geg-tech/brew-keeb/Production/top shell left half.stl

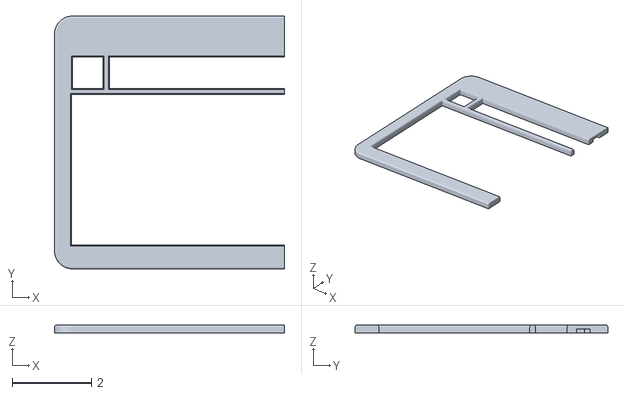
[picture p15: CAD file, 2026-03-29]
Production/top shell left half.stl
5.79 x 6.37 x 0.2
