geg-tech/brew-keeb/CAD/Split Parts/top shell right half.step

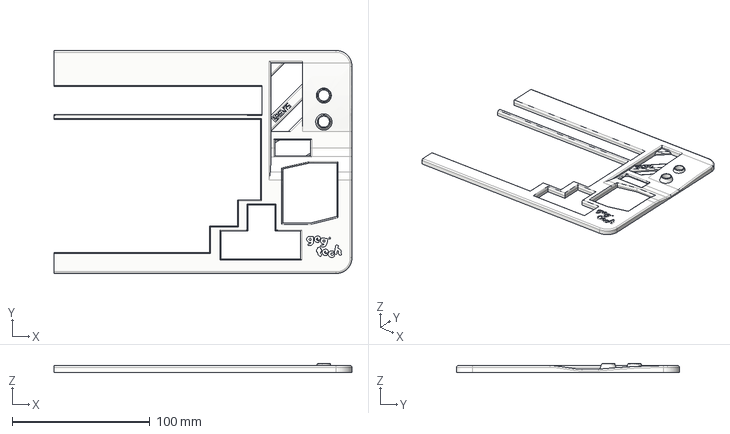
[picture p16: CAD file, 2026-03-26]
CAD/Split Parts/top shell right half.step
216.2 x 161.8 x 6.67 mm
