geg-tech/brew-keeb/Production/plate right half.stl

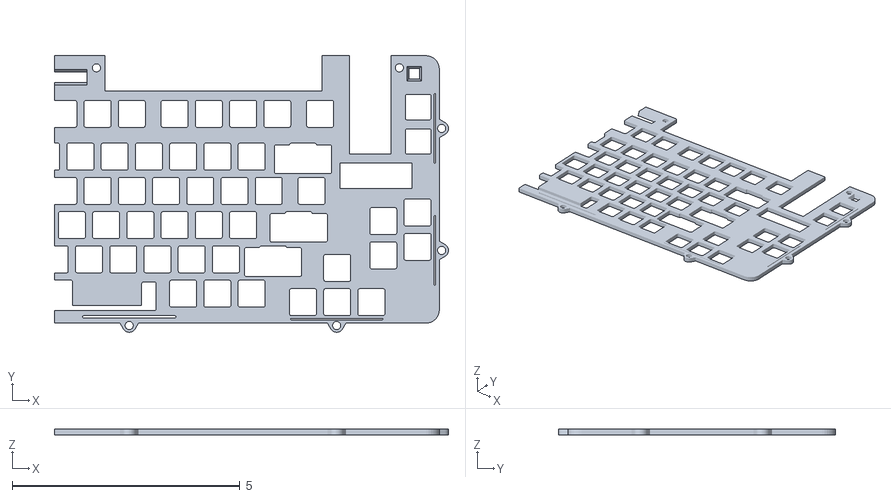
[picture p17: CAD file, 2026-03-29]
Production/plate right half.stl
8.64 x 6.07 x 0.125
