geg-tech/brew-keeb/Production/bottom shell left hald.stl

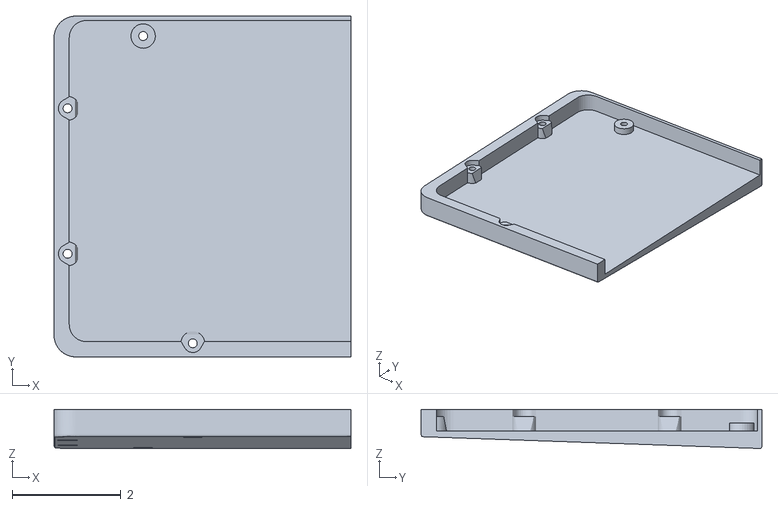
[picture p18: CAD file, 2026-03-29]
Production/bottom shell left hald.stl
5.46 x 6.27 x 0.718
