geg-tech/brew-keeb/Production/knob v3.stl

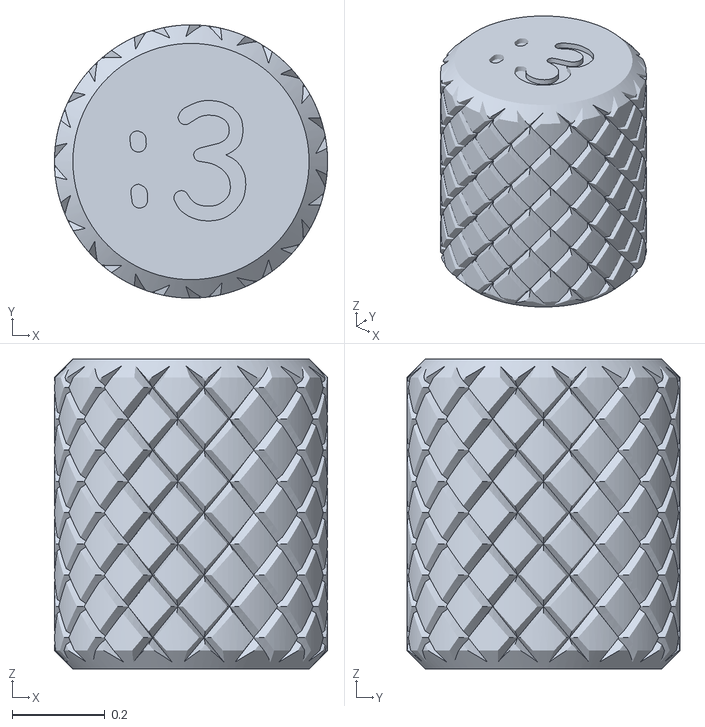
[picture p19: CAD file, 2026-03-29]
Production/knob v3.stl
0.591 x 0.591 x 0.67
