geg-tech/brew-keeb/PCB/brew-keeb-v2.kicad_sch

## KiCad design PCB/brew-keeb-v2.kicad_sch (2026-03-29)

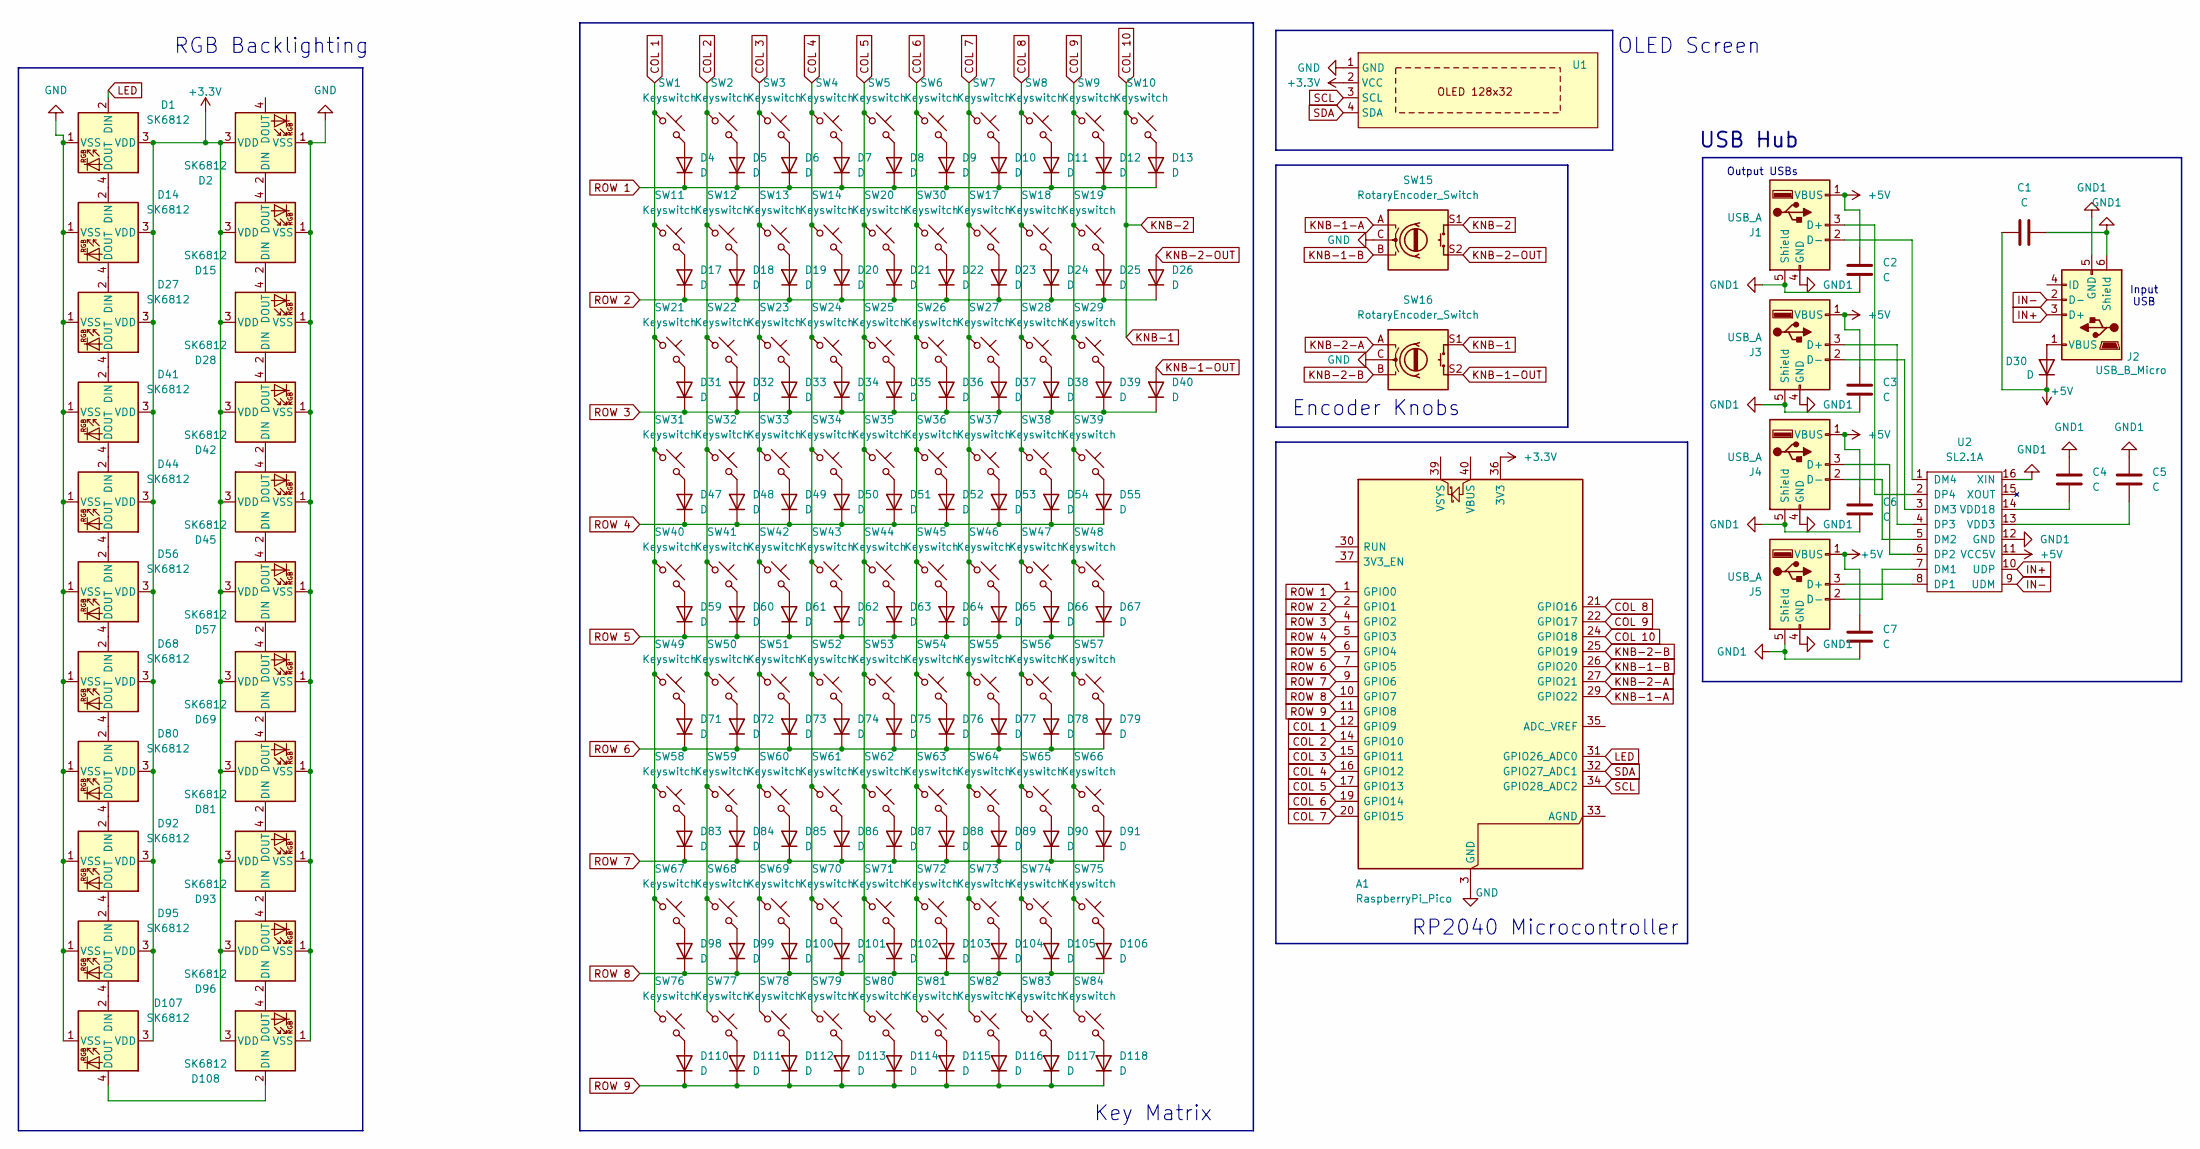
[picture p20: schematic brew-keeb-v2.kicad_sch]

Parts:
A1: RaspberryPi_Pico; RaspberryPi_Pico_Common_Unspecified
C1, C2, C3, C4, C5, C6, C7: C; C_1206_3216Metric_Pad1.33x1.80mm_HandSolder
D1, D2, D14, D15, D27, D28, D41, D42, D44, D45, D56, D57, D68, D69, D80, D81, D92, D93, D95, D96, D107, D108: SK6812; LED_SK6812_PLCC4_5.0x5.0mm_P3.2mm
D4, D5, D6, D7, D8, D9, D10, D11, D12, D13, D17, D18, D19, D20, D21, D22, D23, D24, D25, D26, D30, D31, D32, D33, D34, D35, D36, D37, D38, D39, D40, D47, D48, D49, D50, D51, D52, D53, D54, D55, D59, D60, D61, D62, D63, D64, D65, D66, D67, D71, D72, D73, D74, D75, D76, D77, D78, D79, D83, D84, D85, D86, D87, D88, D89, D90, D91, D98, D99, D100, D101, D102, D103, D104, D105, D106, D110, D111, D112, D113, D114, D115, D116, D117, D118: D; D_DO-35_SOD27_P7.62mm_Horizontal
J1, J3, J4, J5: USB_A; USB_A_Molex_67643_Horizontal
J2: USB_B_Micro; USB_Micro-B_Wuerth_629105150521
SW1, SW2, SW3, SW4, SW5, SW6, SW7, SW8, SW9, SW10, SW11, SW12, SW13, SW14, SW17, SW18, SW19, SW20, SW21, SW22, SW23, SW24, SW25, SW26, SW27, SW28, SW29, SW30, SW31, SW32, SW33, SW34, SW35, SW36, SW37, SW38, SW39, SW40, SW41, SW42, SW43, SW44, SW45, SW46, SW47, SW48, SW49, SW50, SW51, SW52, SW53, SW54, SW55, SW56, SW57, SW58, SW59, SW60, SW61, SW62, SW63, SW64, SW65, SW66, SW67, SW68, SW69, SW70, SW71, SW72, SW73, SW74, SW75, SW76, SW77, SW78, SW79, SW80, SW81, SW82, SW83, SW84: Keyswitch; SW_Cherry_MX_1.00u_PCB
SW15, SW16: RotaryEncoder_Switch; RotaryEncoder_Alps_EC11E-Switch_Vertical_H20mm
U1: SSD1306-0.91-OLED-4pin-128x32
U2: SL2.1A; SOIC-16_4.55x10.3mm_P1.27mm

Connections:
+3.3V: A1.36 (3V3), D1.3 (VDD), D2.3 (VDD), D14.3 (VDD), D15.3 (VDD), D27.3 (VDD), D28.3 (VDD), D41.3 (VDD), D42.3 (VDD), D44.3 (VDD), D45.3 (VDD), D56.3 (VDD), D57.3 (VDD), D68.3 (VDD), D69.3 (VDD), D80.3 (VDD), D81.3 (VDD), D92.3 (VDD), D93.3 (VDD), D95.3 (VDD), D96.3 (VDD), D107.3 (VDD), D108.3 (VDD), U1.2 (VCC)
+5V: C1.1, C2.1, C3.1, C6.1, C7.1, D30.1 (K), J1.1 (VBUS), J3.1 (VBUS), J4.1 (VBUS), J5.1 (VBUS), U2.11 (VCC5V)
COL 1: A1.12 (GPIO9), SW1.1, SW11.1, SW21.1, SW31.1, SW40.1, SW49.1, SW58.1, SW67.1, SW76.1
COL 2: A1.14 (GPIO10), SW2.1, SW12.1, SW22.1, SW32.1, SW41.1, SW50.1, SW59.1, SW68.1, SW77.1
COL 3: A1.15 (GPIO11), SW3.1, SW13.1, SW23.1, SW33.1, SW42.1, SW51.1, SW60.1, SW69.1, SW78.1
COL 4: A1.16 (GPIO12), SW4.1, SW14.1, SW24.1, SW34.1, SW43.1, SW52.1, SW61.1, SW70.1, SW79.1
COL 5: A1.17 (GPIO13), SW5.1, SW20.1, SW25.1, SW35.1, SW44.1, SW53.1, SW62.1, SW71.1, SW80.1
COL 6: A1.19 (GPIO14), SW6.1, SW26.1, SW30.1, SW36.1, SW45.1, SW54.1, SW63.1, SW72.1, SW81.1
COL 7: A1.20 (GPIO15), SW7.1, SW17.1, SW27.1, SW37.1, SW46.1, SW55.1, SW64.1, SW73.1, SW82.1
COL 8: A1.21 (GPIO16), SW8.1, SW18.1, SW28.1, SW38.1, SW47.1, SW56.1, SW65.1, SW74.1, SW83.1
COL 9: A1.22 (GPIO17), SW9.1, SW19.1, SW29.1, SW39.1, SW48.1, SW57.1, SW66.1, SW75.1, SW84.1
COL 10: A1.24 (GPIO18), SW10.1, SW15.S1, SW16.S1
GND: A1.3 (GND), A1.8 (GND), A1.13 (GND), A1.18 (GND), A1.23 (GND), A1.28 (GND), A1.38 (GND), D1.1 (VSS), D2.1 (VSS), D14.1 (VSS), D15.1 (VSS), D27.1 (VSS), D28.1 (VSS), D41.1 (VSS), D42.1 (VSS), D44.1 (VSS), D45.1 (VSS), D56.1 (VSS), D57.1 (VSS), D68.1 (VSS), D69.1 (VSS), D80.1 (VSS), D81.1 (VSS), D92.1 (VSS), D93.1 (VSS), D95.1 (VSS), D96.1 (VSS), D107.1 (VSS), D108.1 (VSS), SW15.C, SW16.C, U1.1 (GND)
GND1: C1.2, C2.2, C3.2, C4.2, C5.2, C6.2, C7.2, J1.4 (GND), J1.5 (Shield), J2.5 (GND), J2.6 (Shield), J3.4 (GND), J3.5 (Shield), J4.4 (GND), J4.5 (Shield), J5.4 (GND), J5.5 (Shield), U2.12 (GND), U2.16 (XIN)
IN+: J2.3 (D+), U2.10 (UDP)
IN-: J2.2 (D-), U2.9 (UDM)
KNB-1-A: A1.29 (GPIO22), SW15.A
KNB-1-B: A1.26 (GPIO20), SW15.B
KNB-1-OUT: D40.2 (A), SW16.S2
KNB-2-A: A1.27 (GPIO21), SW16.A
KNB-2-B: A1.25 (GPIO19), SW16.B
KNB-2-OUT: D26.2 (A), SW15.S2
LED: A1.31 (GPIO26_ADC0), D1.2 (DIN)
unnamed: C4.1, U2.14 (VDD18)
unnamed: C5.1, U2.13 (VDD3)
unnamed: D1.4 (DOUT), D14.2 (DIN)
unnamed: D4.2 (A), SW1.2
unnamed: D5.2 (A), SW2.2
unnamed: D6.2 (A), SW3.2
unnamed: D7.2 (A), SW4.2
unnamed: D8.2 (A), SW5.2
unnamed: D9.2 (A), SW6.2
unnamed: D10.2 (A), SW7.2
unnamed: D11.2 (A), SW8.2
unnamed: D12.2 (A), SW9.2
unnamed: D13.2 (A), SW10.2
unnamed: D14.4 (DOUT), D27.2 (DIN)
unnamed: D15.2 (DIN), D28.4 (DOUT)
unnamed: D2.2 (DIN), D15.4 (DOUT)
unnamed: D17.2 (A), SW11.2
unnamed: D18.2 (A), SW12.2
unnamed: D19.2 (A), SW13.2
unnamed: D20.2 (A), SW14.2
unnamed: D21.2 (A), SW20.2
unnamed: D22.2 (A), SW30.2
unnamed: D23.2 (A), SW17.2
unnamed: D24.2 (A), SW18.2
unnamed: D25.2 (A), SW19.2
unnamed: D27.4 (DOUT), D41.2 (DIN)
unnamed: D28.2 (DIN), D42.4 (DOUT)
unnamed: D30.2 (A), J2.1 (VBUS)
unnamed: D31.2 (A), SW21.2
unnamed: D32.2 (A), SW22.2
unnamed: D33.2 (A), SW23.2
unnamed: D34.2 (A), SW24.2
unnamed: D35.2 (A), SW25.2
unnamed: D36.2 (A), SW26.2
unnamed: D37.2 (A), SW27.2
unnamed: D38.2 (A), SW28.2
unnamed: D39.2 (A), SW29.2
unnamed: D41.4 (DOUT), D44.2 (DIN)
unnamed: D42.2 (DIN), D45.4 (DOUT)
unnamed: D44.4 (DOUT), D56.2 (DIN)
unnamed: D45.2 (DIN), D57.4 (DOUT)
unnamed: D47.2 (A), SW31.2
unnamed: D48.2 (A), SW32.2
unnamed: D49.2 (A), SW33.2
unnamed: D50.2 (A), SW34.2
unnamed: D51.2 (A), SW35.2
unnamed: D52.2 (A), SW36.2
unnamed: D53.2 (A), SW37.2
unnamed: D54.2 (A), SW38.2
unnamed: D55.2 (A), SW39.2
unnamed: D56.4 (DOUT), D68.2 (DIN)
unnamed: D57.2 (DIN), D69.4 (DOUT)
unnamed: D59.2 (A), SW40.2
unnamed: D60.2 (A), SW41.2
unnamed: D61.2 (A), SW42.2
unnamed: D62.2 (A), SW43.2
unnamed: D63.2 (A), SW44.2
unnamed: D64.2 (A), SW45.2
unnamed: D65.2 (A), SW46.2
unnamed: D66.2 (A), SW47.2
unnamed: D67.2 (A), SW48.2
unnamed: D68.4 (DOUT), D80.2 (DIN)
unnamed: D69.2 (DIN), D81.4 (DOUT)
unnamed: D71.2 (A), SW49.2
unnamed: D72.2 (A), SW50.2
unnamed: D73.2 (A), SW51.2
unnamed: D74.2 (A), SW52.2
unnamed: D75.2 (A), SW53.2
unnamed: D76.2 (A), SW54.2
unnamed: D77.2 (A), SW55.2
unnamed: D78.2 (A), SW56.2
unnamed: D79.2 (A), SW57.2
unnamed: D80.4 (DOUT), D92.2 (DIN)
unnamed: D81.2 (DIN), D93.4 (DOUT)
unnamed: D83.2 (A), SW58.2
unnamed: D84.2 (A), SW59.2
unnamed: D85.2 (A), SW60.2
unnamed: D86.2 (A), SW61.2
unnamed: D87.2 (A), SW62.2
unnamed: D88.2 (A), SW63.2
unnamed: D89.2 (A), SW64.2
unnamed: D90.2 (A), SW65.2
unnamed: D91.2 (A), SW66.2
unnamed: D92.4 (DOUT), D95.2 (DIN)
unnamed: D93.2 (DIN), D96.4 (DOUT)
unnamed: D98.2 (A), SW67.2
unnamed: D99.2 (A), SW68.2
unnamed: D100.2 (A), SW69.2
unnamed: D101.2 (A), SW70.2
unnamed: D102.2 (A), SW71.2
unnamed: D103.2 (A), SW72.2
unnamed: D104.2 (A), SW73.2
unnamed: D105.2 (A), SW74.2
unnamed: D106.2 (A), SW75.2
unnamed: D95.4 (DOUT), D107.2 (DIN)
unnamed: D107.4 (DOUT), D108.2 (DIN)
unnamed: D96.2 (DIN), D108.4 (DOUT)
unnamed: D110.2 (A), SW76.2
unnamed: D111.2 (A), SW77.2
unnamed: D112.2 (A), SW78.2
unnamed: D113.2 (A), SW79.2
unnamed: D114.2 (A), SW80.2
unnamed: D115.2 (A), SW81.2
unnamed: D116.2 (A), SW82.2
unnamed: D117.2 (A), SW83.2
unnamed: D118.2 (A), SW84.2
unnamed: J1.2 (D-), U2.1 (DM4)
unnamed: J1.3 (D+), U2.2 (DP4)
unnamed: J3.2 (D-), U2.3 (DM3)
unnamed: J3.3 (D+), U2.4 (DP3)
unnamed: J4.2 (D-), U2.5 (DM2)
unnamed: J4.3 (D+), U2.6 (DP2)
unnamed: J5.2 (D-), U2.7 (DM1)
unnamed: J5.3 (D+), U2.8 (DP1)
ROW 1: A1.1 (GPIO0), D4.1 (K), D5.1 (K), D6.1 (K), D7.1 (K), D8.1 (K), D9.1 (K), D10.1 (K), D11.1 (K), D12.1 (K), D13.1 (K)
ROW 2: A1.2 (GPIO1), D17.1 (K), D18.1 (K), D19.1 (K), D20.1 (K), D21.1 (K), D22.1 (K), D23.1 (K), D24.1 (K), D25.1 (K), D26.1 (K)
ROW 3: A1.4 (GPIO2), D31.1 (K), D32.1 (K), D33.1 (K), D34.1 (K), D35.1 (K), D36.1 (K), D37.1 (K), D38.1 (K), D39.1 (K), D40.1 (K)
ROW 4: A1.5 (GPIO3), D47.1 (K), D48.1 (K), D49.1 (K), D50.1 (K), D51.1 (K), D52.1 (K), D53.1 (K), D54.1 (K), D55.1 (K)
ROW 5: A1.6 (GPIO4), D59.1 (K), D60.1 (K), D61.1 (K), D62.1 (K), D63.1 (K), D64.1 (K), D65.1 (K), D66.1 (K), D67.1 (K)
ROW 6: A1.7 (GPIO5), D71.1 (K), D72.1 (K), D73.1 (K), D74.1 (K), D75.1 (K), D76.1 (K), D77.1 (K), D78.1 (K), D79.1 (K)
ROW 7: A1.9 (GPIO6), D83.1 (K), D84.1 (K), D85.1 (K), D86.1 (K), D87.1 (K), D88.1 (K), D89.1 (K), D90.1 (K), D91.1 (K)
ROW 8: A1.10 (GPIO7), D98.1 (K), D99.1 (K), D100.1 (K), D101.1 (K), D102.1 (K), D103.1 (K), D104.1 (K), D105.1 (K), D106.1 (K)
ROW 9: A1.11 (GPIO8), D110.1 (K), D111.1 (K), D112.1 (K), D113.1 (K), D114.1 (K), D115.1 (K), D116.1 (K), D117.1 (K), D118.1 (K)
SCL: A1.34 (GPIO28_ADC2), U1.3 (SCL)
SDA: A1.32 (GPIO27_ADC1), U1.4 (SDA)

Notes on the sheet:
RP2040 Microcontroller
Key Matrix
USB Hub
Encoder Knobs
Input USB
Output USBs
OLED Screen
RGB Backlighting
